jebentancour/topsulin/state.h

#include <stdint.h>
#include <stdio.h>
#include <stdbool.h>

typedef enum {
    button_pressed,
    long_button_pressed,
    double_button_pressed,
    encoder_update
} event_t;

void state_init(void);

void state_idle_set_flag(volatile uint8_t* main_idle_flag);

void state_display_set_flag(volatile uint8_t* main_display_flag);

void state_process_display(void);

void state_on_event(event_t event);

void state_show_pin(char* pin);

void state_show_pin_error(void);

void state_show_pin_ok(void);

void state_update_config(void);

void state_begin(void);

void state_clock_set(void);

void state_gls_write(void);

void state_sleep(void);

void state_set_bt_state(uint8_t state);

void state_update_mem(void);
