jebentancour/topsulin/epd/ImageData.c

/**
 *  @filename   :   imagedata.cpp
 *  @brief      :   data file for epd demo
 *
 *  Copyright (C) Waveshare     September 5 2017
 *
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
 * THE SOFTWARE IS PROVIDED "AS IS", WITHOUT WARRANTY OF ANY KIND, EXPRESS OR
 * IMPLIED, INCLUDING BUT NOT LIMITED TO THE WARRANTIES OF MERCHANTABILITY,
 * FITNESS OR A PARTICULAR PURPOSE AND NONINFRINGEMENT. IN NO EVENT SHALL THE
 * AUTHORS OR COPYRIGHT HOLDERS BE LIABLE FOR ANY CLAIM, DAMAGES OR OTHER
 * LIABILITY WHETHER IN AN ACTION OF CONTRACT, TORT OR OTHERWISE, ARISING FROM,
 * OUT OF OR IN CONNECTION WITH THE SOFTWARE OR THE USE OR OTHER DEALINGS IN
 * THE SOFTWARE.
 */

#include "ImageData.h"

const unsigned char gImage_icon_low_16[32] = {
  0xff,0xff
 ,0xff,0xff
 ,0xc0,0x0F
 ,0x80,0x07
 ,0x9f,0xe7
 ,0x9f,0xe3
 ,0x9f,0xe3
 ,0x9f,0xe3
 ,0x9f,0xe7
 ,0x80,0x07
 ,0xc0,0x0F
 ,0xff,0xff
 ,0xff,0xff
 ,0xfa,0x1f
 ,0xff,0xff
 ,0xff,0xff
};

const unsigned char gImage_icon_bt_16[32] = {
 0xff,0xff
,0xff,0xff
,0xf7,0xef
,0xf3,0xcf
,0xf9,0x9f
,0x80,0x01
,0x80,0x01
,0xcc,0x33
,0xe1,0x87
,0xf3,0xcf
,0xfe,0x7f
,0xff,0xff
,0xfb,0xdf
,0xfc,0x3f
,0xff,0xff
,0xff,0xff
};

const unsigned char gImage_icon_dev_16[32] = {
 0xff,0xff
,0xff,0xff
,0xff,0xff
,0xc0,0x03
,0x80,0x01
,0x8f,0xf9
,0x8f,0xf9
,0xaf,0xf9
,0xaf,0xf9
,0x8f,0xf9
,0x8f,0xf9
,0x80,0x01
,0xc0,0x03
,0xff,0xff
,0xff,0xff
,0xff,0xff
};

const unsigned char gImage_icon_mem_16[32] = {
 0xff,0xff
,0xff,0xff
,0xc0,0x03
,0xc0,0x03
,0xc0,0x3b
,0xc0,0x3b
,0xcc,0x3b
,0xde,0x3b
,0xde,0x3b
,0xcc,0x3b
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
,0xff,0xff,0xff,0xff,0xff,0x83,0xf0,0x00,0x00,0xf8,0x7f,0xff,0xff,0xff,0xff,0xc0
,0xff,0xff,0xff,0xff,0xff,0x87,0xe0,0x00,0x00,0x78,0x7f,0xff,0xff,0xff,0xff,0xc0
,0xff,0xff,0xff,0xff,0xff,0x87,0xe0,0x00,0x00,0x38,0x7f,0xff,0xff,0xff,0xff,0xc0
,0xff,0xff,0xff,0xff,0xff,0x87,0xe0,0x00,0x00,0x18,0x3f,0xff,0xff,0xff,0xff,0xc0
,0xff,0xff,0xff,0xff,0xff,0x87,0xe0,0x00,0x00,0x18,0x3f,0xff,0xff,0xff,0xff,0xc0
,0xff,0xff,0xff,0xff,0xff,0x87,0xe0,0x00,0x00,0x38,0x7f,0xff,0xff,0xff,0xff,0xc0
,0xff,0xff,0xff,0xff,0xff,0x87,0xe0,0x00,0x00,0x78,0x7f,0xff,0xff,0xff,0xff,0xc0
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
};
