jebentancour/topsulin/ble_services.h

#include <stdint.h>

#include "ble_gls.h"

void ble_services_init(void);

void add_glucose_measurement(ble_gls_rec_t rec);

void time_ble_update(void);

void batt_ble_update(uint16_t v);

void peer_manager_erase_bonds(void);

void advertising_start(void);

void advertising_stop(void);

void advertising_toggle(void);
